CDFER/KEX/KEX1/PCB V1/Graphics/600a559d4a0e4b1431ca76a25d37b9f6.jpg

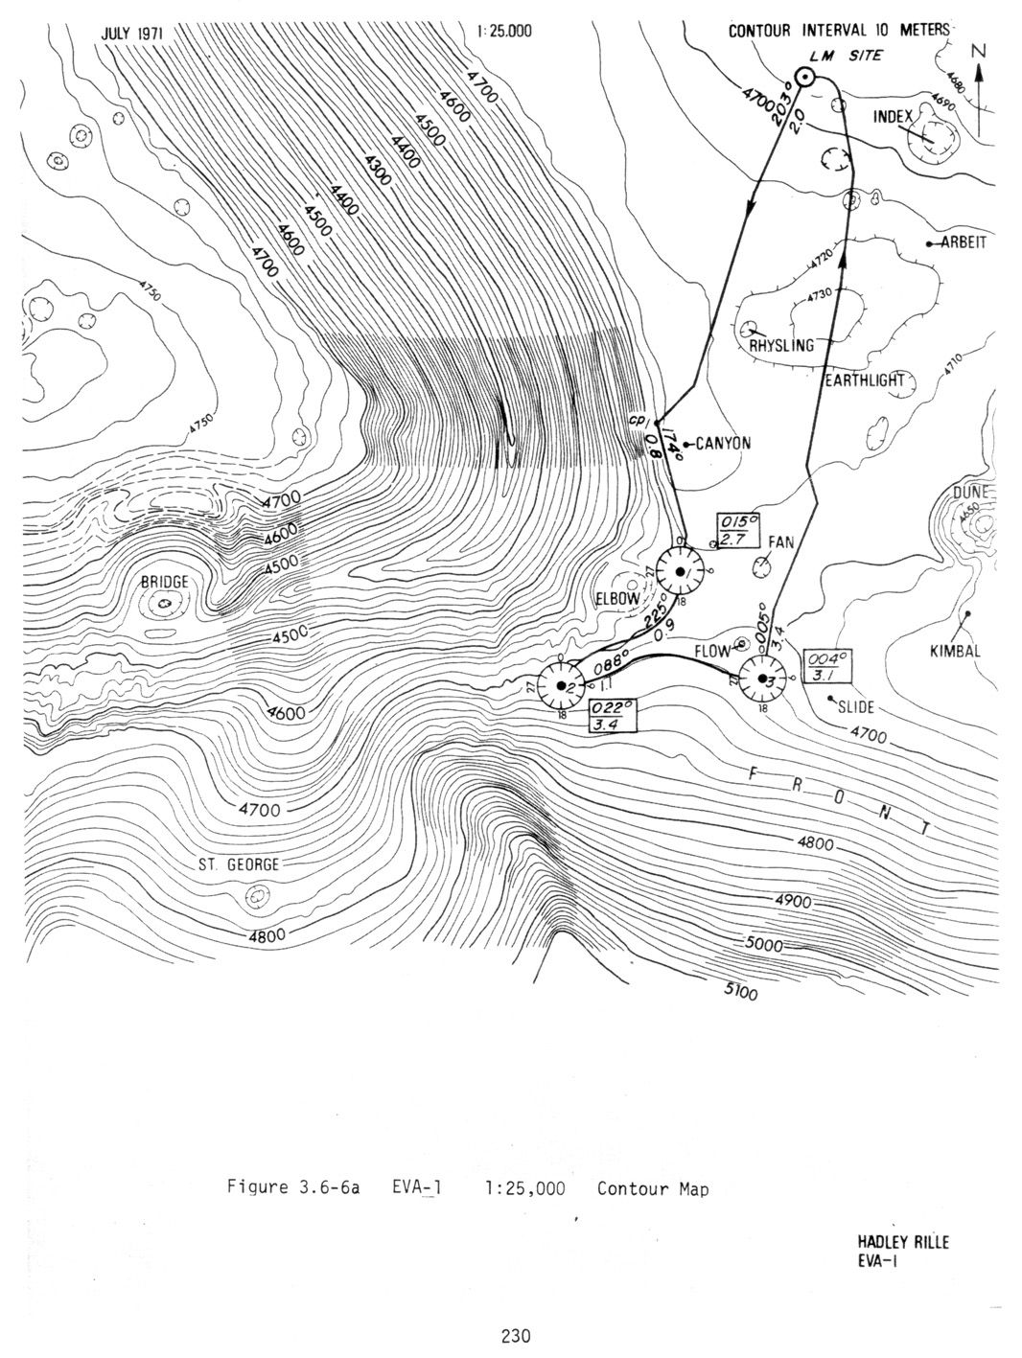
KEX1/PCB V1/Graphics/600a559d4a0e4b1431ca76a25d37b9f6.jpg
