CDFER/KEX/KEX1/PCB V1/Graphics/a15.lsp236.jpg

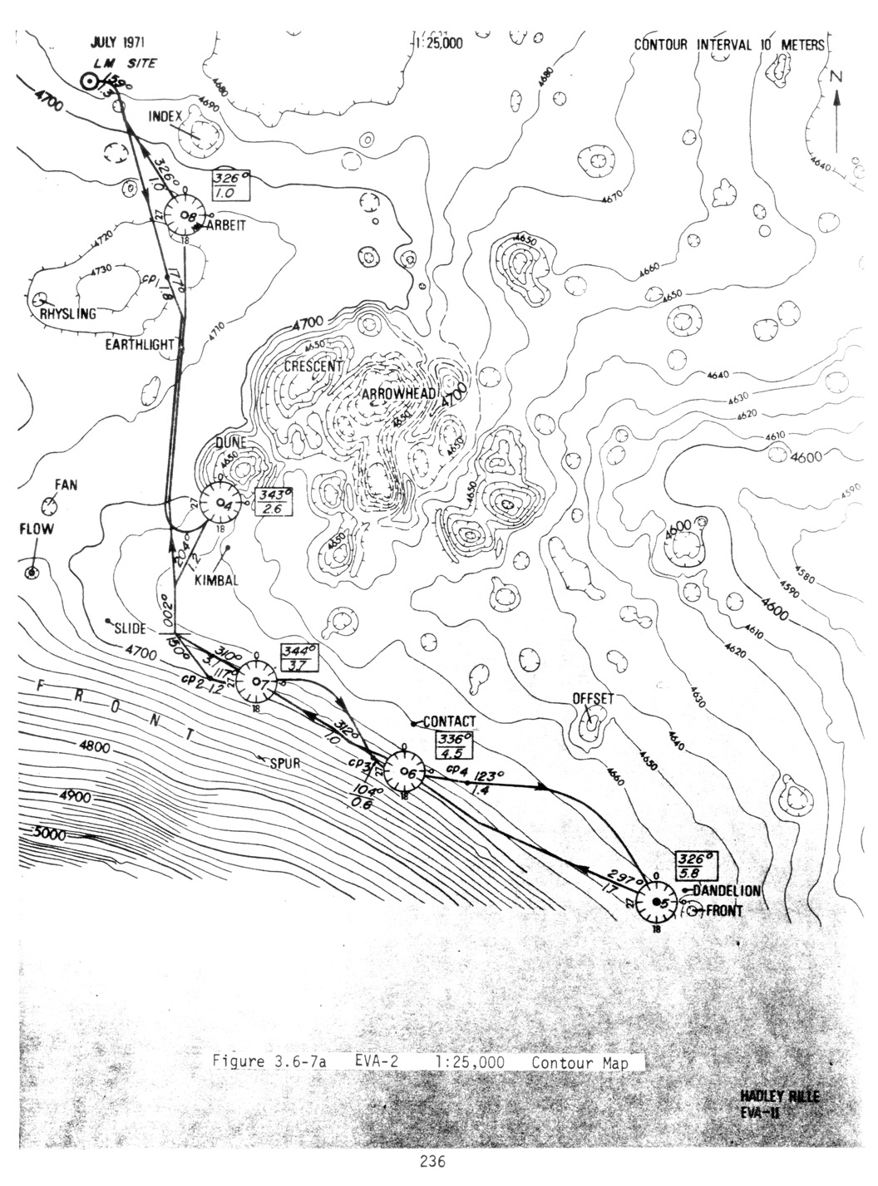
KEX1/PCB V1/Graphics/a15.lsp236.jpg
