CDFER/KEX/KEX1/PCB V1/Graphics/IO04.png

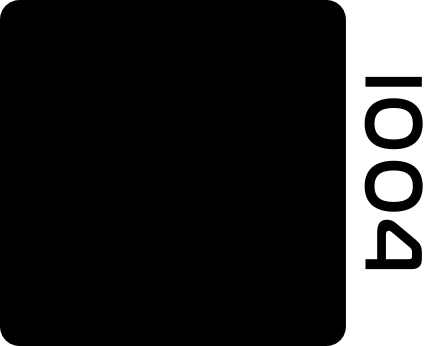
KEX1/PCB V1/Graphics/IO04.png
